shopped/OSOS/CADfiles/FacePlate.SLDPRT

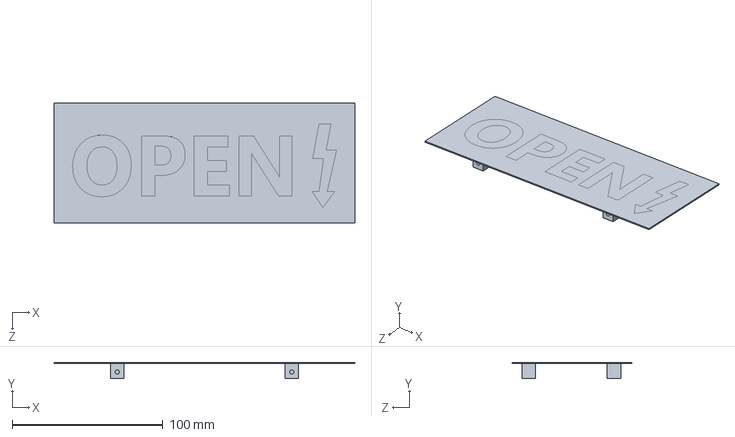
[picture p13: CAD file, 2023-03-21]
CADfiles/FacePlate.SLDPRT
200.0 x 10.9 x 80.0 mm
