shopped/OSOS/CADfiles/sg90-micro-servo-9g-tower-pro-1.snapshot.3/SG90 - Micro Servo 9g - Tower Pro.1.SLDPRT

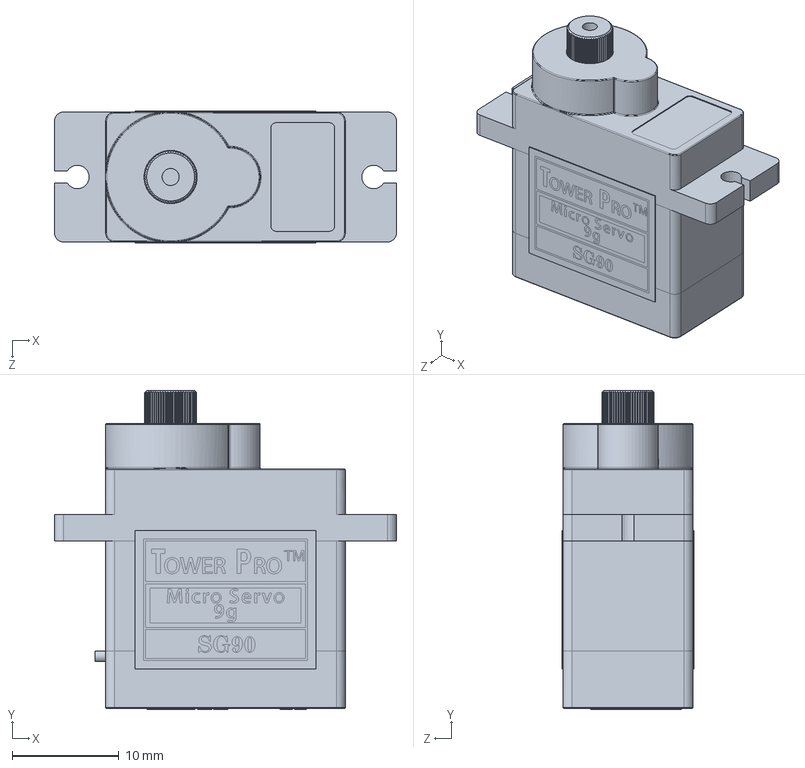
[picture p14: CAD file, 2023-05-09]
CADfiles/sg90-micro-servo-9g-tower-pro-1.snapshot.3/SG90 - Micro Servo 9g - Tower Pro.1.SLDPRT
32.1 x 30.0 x 12.4 mm
