shopped/OSOS/CADfiles/ChipBracket.SLDPRT

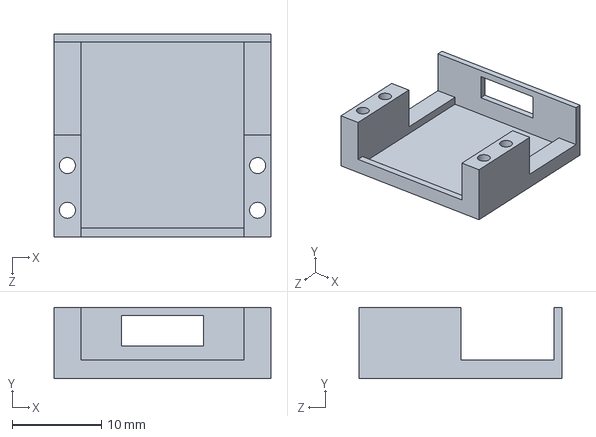
[picture p15: CAD file, 2023-03-21]
CADfiles/ChipBracket.SLDPRT
24.3 x 8.00 x 22.7 mm
