shopped/OSOS/CADfiles/sg90-micro-servo-9g-tower-pro-1.snapshot.3/SG90 - Micro Servo 9g - Tower Pro.3.SLDPRT

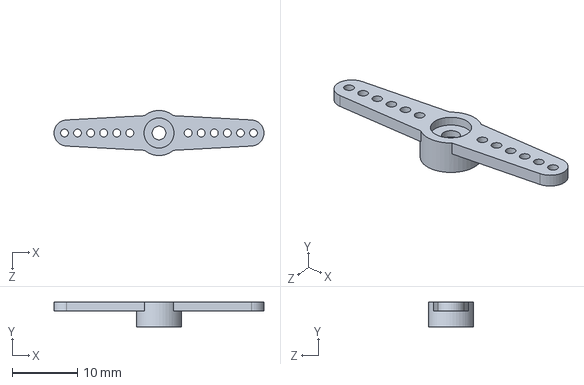
[picture p16: CAD file, 2023-05-09]
CADfiles/sg90-micro-servo-9g-tower-pro-1.snapshot.3/SG90 - Micro Servo 9g - Tower Pro.3.SLDPRT
32.1 x 3.80 x 6.90 mm
