shopped/OSOS/CADfiles/chip/chip.step

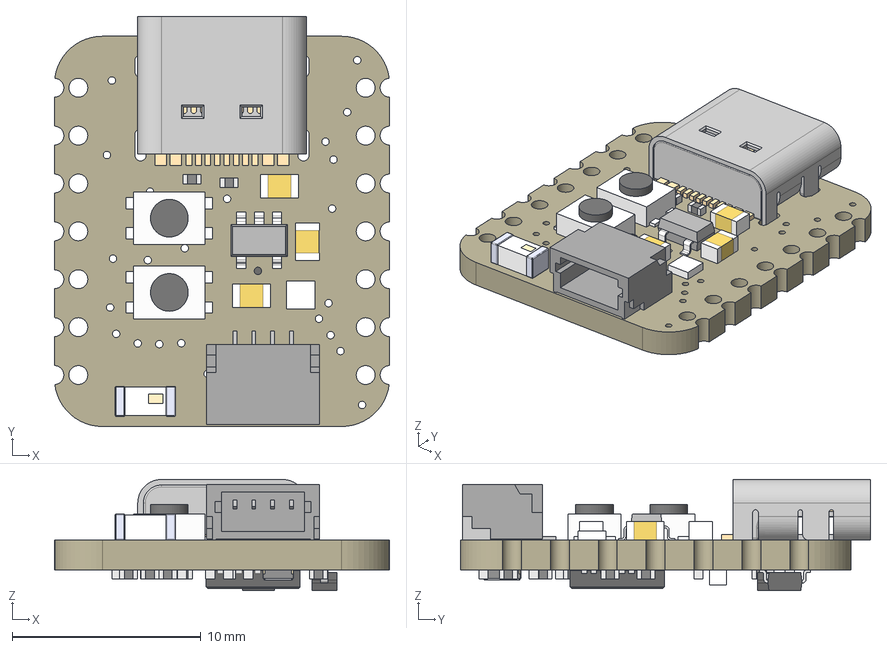
[picture p17: CAD file, 2023-03-21]
CADfiles/chip/chip.step
17.8 x 21.7 x 5.89 mm
Board
22uF x 3
reset
USB TYPE C
1k x 18
STEMMA_I2C_QTSKINNY
AP2112K-3.3
WS2812B_SK6805_1515
NSR0320 x 2
0 ohm x 2
40MHz
2.4GHz
BOOT0
ESP32-C3FH4
10K
